samidh93/stereolithography-3d-printer/Inc/SchrittMotor_Y.h

/*
 * SchrittMotor_Y.h
 *
 *  Created on: 10.12.2019
 *      Author: Home
 */

#ifndef SCHRITTMOTOR_Y_H_
#define SCHRITTMOTOR_Y_H_

#include "stm32f3xx_hal.h"

void Stepper_Y_Achse(void);


#endif /* SCHRITTMOTOR_Y_H_ */
