samidh93/stereolithography-3d-printer/Inc/FIR_5Order_RingBuffer.h

/*
 * FIR_5Order_RingBuffer.h
 *
 *  Created on: 10.12.2019
 *  Author: Sami
 */

#ifndef FIR_5ORDER_RINGBUFFER_H_
#define FIR_5ORDER_RINGBUFFER_H_

float FIR_5_RingBuffer(float new_value);


#endif /* FIR_5ORDER_RINGBUFFER_H_ */
