samidh93/stereolithography-3d-printer/Inc/Filter_3_Order.h

/*
 * Filter_3_Order.h
 *  Created on: 08.12.2019
 *  Author: Home
 */

#ifndef FILTER_3_ORDER_H_
#define FILTER_3_ORDER_H_

float Filter_FIR_3_Order (float FIR_Value);


#endif /* FILTER_3_ORDER_H_ */
