samidh93/stereolithography-3d-printer/Inc/Temperatur_Regelung.h

/*
 * Temperatur_Regelung.h
 *
 *  Created on: 07.12.2019
 *      Author: Home
 */


#ifndef TEMPERATUR_REGELUNG_H_
#define TEMPERATUR_REGELUNG_H_

void Temperatur_Polymer_Regler(ADC_HandleTypeDef *hadc4, TIM_HandleTypeDef *htim15);


#endif /* TEMPERATUR_REGELUNG_H_ */
